CraftPwr/CPRPS24V3A/testing/CP-RPS-24V-3A Testing Documentation.md

**CP-RPS-24V-3A Test Documentation**  
This document presents a concise summary of the testing conducted on our proof of concept (POC). The tests encompass all factors influencing the test environment and are carried out from minimum to maximum thresholds.  
****  
An image of the test environment of the POC

**No-Load Test**   
Noise testing of the DC-DC converter is conducted with no load connected to the device's output. The test environment includes an oscilloscope set to 20 Hz in AC coupling mode. The power outlet supplies current to all devices in the room, including lights, the oscilloscope, and the power supply. The expected Noise outcome at No Load connected is below 50mV RMS

1. **32V Input / 0V Output**

At 0V the Input (yellow waveform) noise of 5.02mV, is filtered to 1.68mV at Output (blue waveform). This shows that the filtering capacity of the DC-DC Converter is exceptional.  
****

2. **32V Input / 5V Output**

At 5V the Input (yellow waveform) noise of 3.74mV, is 338mV at Output (blue waveform).   
There is a Ripple at the Output up to 5V range. This ripple is caused by the \-5V regulation, as the main DC-DC converter operates from above 5V. To achieve an output range of 0V to 25V, we utilize the \-5V regulator.





3. **32V Input / 10V Output**

At 10V the Input (yellow waveform) noise of 4.18mV, is filtered to 2.56mV at Output (blue waveform). 

****

4. **32V Input / 15V Output**

At 15V the Input (yellow waveform) noise of 4.18mV, is filtered to 2.56mV at Output (blue waveform). 



5. **32V Input / 20V Output**

At 20V the Input (yellow waveform) noise of 9.34mV, is filtered to 5.21mV at Output (blue waveform). 

****

6. **32V Input / 25V Output**

At 25V the Input (yellow waveform) noise of 9.34mV, is filtered to 5.21mV at Output (blue waveform). 

****

**LOADED TEST**  
Noise testing of DC-DC Converter when a Load (Battery) is connected across the output of the device

1. **32V Input / 14V Output**

At 14V the Input (yellow waveform) noise of 230mV, is filtered to 32.6mV at Output (blue waveform). 

****

**STABILITY TEST**  
Link for the test results: 
This sheet provides a complete report of the stability test of the version 2 of the DC-DC Module of the Power supply. Test values were collected for each voltage level, ranging from 0 to 25 volts, and for current levels ranging from 0 to 3 amperes, with an incremental difference of 100 milliamperes.

[image1]: <>

[image2]: <>

[image3]: <>

[image4]: <>

[image5]: <>

[image6]: <>

[image7]: <>

[image8]: <>

[image9]: <>
